petterssonandreas/cooking_thermometer/apps/ct/src/display.c

#include "display.h"

#include <zephyr/kernel.h>
#include <zephyr/device.h>
#include <zephyr/display/cfb.h>
#include <zephyr/drivers/display.h>
#include <stdio.h>

#include <zephyr/logging/log.h>
LOG_MODULE_REGISTER(ct_display, CONFIG_CT_DISPLAY_LOG_LEVEL);

#include "cttime.h"
#include "state.h"

#define FONT_IDX 1

static const struct device *dev = DEVICE_DT_GET(DT_CHOSEN(zephyr_display));

static K_THREAD_STACK_DEFINE(display_thread_stack, 1024);

static struct k_thread display_thread;


static void display_draw_no_probe(void)
{
    char s[16];
    snprintf(s, sizeof(s), "---");
    cfb_print(dev, s, 0, 24);
}

static void display_draw_battery_level(uint8_t battery_percentage)
{
    cfb_invert_area(dev, 109, 0, 17, 16);
    cfb_invert_area(dev, 111, 2, 13, 12);
    cfb_invert_area(dev, 126, 5, 2, 6);

    if (battery_percentage > 20) {
        cfb_invert_area(dev, 112, 4, 3, 9);
    }
    if (battery_percentage > 60) {
        cfb_invert_area(dev, 116, 4, 3, 9);
    }
    if (battery_percentage > 80) {
        cfb_invert_area(dev, 120, 4, 3, 9);
    }
}

static void display_fn(void *p1, void *p2, void *p3)
{
    UNUSED(p1);
    UNUSED(p2);
    UNUSED(p3);

    char s[16];

    while (true) {
        k_sleep(K_MSEC(100));

        /* Start by clearing */
        cfb_framebuffer_clear(dev, false);

        snprintf(s, sizeof(s), "%d", state.state);
        cfb_print(dev, s, 0, 0);

        switch (state.state) {
        case STATE_INIT:
            cfb_print(dev, "Init", 0, 24);
            break;

        case STATE_IDLE:
        case STATE_TARGET_TEMP_REACHED:
        case STATE_TARGET_TEMP_REACHED_ACKED:
            if (!state.probe_connected) {
                display_draw_no_probe();
            }
            else {
                display_draw_temperature(state.temperature);
            }
            break;

        case STATE_SET_TARGET_TEMP:
            if (state.blink) {
                snprintf(s, sizeof(s), "% 3d *C", state.target_temperature);
                cfb_print(dev, s, 0, 24);
            }
            break;

        default:
            cfb_print(dev, "state?", 0, 24);
            break;
        }

        display_draw_battery_level(state.battery_percentage);

        /* Do the actual drawing */
        cfb_framebuffer_finalize(dev);
    }
}

int display_init(void)
{
    uint16_t x_res;
    uint16_t y_res;
    uint16_t rows;
    uint8_t ppt;
    uint8_t font_width;
    uint8_t font_height;

    if (!device_is_ready(dev)) {
        LOG_ERR("Device %s not ready", dev->name);
        return -ENODEV;
    }

    if (display_set_pixel_format(dev, PIXEL_FORMAT_MONO10) != 0) {
        if (display_set_pixel_format(dev, PIXEL_FORMAT_MONO01) != 0) {
            LOG_ERR("Failed to set required pixel format");
            return -EINVAL;
        }
    }

    LOG_INF("Initialized %s", dev->name);

    if (cfb_framebuffer_init(dev)) {
        LOG_ERR("Framebuffer initialization failed!");
        return -ENODEV;
    }

    cfb_framebuffer_clear(dev, true);

    display_blanking_off(dev);

    x_res = cfb_get_display_parameter(dev, CFB_DISPLAY_WIDTH);
    y_res = cfb_get_display_parameter(dev, CFB_DISPLAY_HEIGH);
    rows = cfb_get_display_parameter(dev, CFB_DISPLAY_ROWS);
    ppt = cfb_get_display_parameter(dev, CFB_DISPLAY_PPT);

    if (cfb_get_font_size(dev, FONT_IDX, &font_width, &font_height))
    {
        LOG_ERR("Failed to get font for index %u", FONT_IDX);
        return -EBFONT;
    }
    cfb_framebuffer_set_font(dev, FONT_IDX);
    LOG_INF("font width %d, font height %d", font_width, font_height);

    LOG_INF("x_res %d, y_res %d, ppt %d, rows %d, cols %d", x_res, y_res, ppt, rows, cfb_get_display_parameter(dev, CFB_DISPLAY_COLS));

    // cfb_framebuffer_invert(dev);

    cfb_set_kerning(dev, 0);

    cfb_framebuffer_clear(dev, false);
    cfb_print(dev, "Booting", 0, 24);
    cfb_framebuffer_finalize(dev);

    /* Start display thread */
    k_thread_create(
        &display_thread,
        display_thread_stack,
        K_THREAD_STACK_SIZEOF(display_thread_stack),
        display_fn,
        NULL, NULL, NULL,
        K_LOWEST_APPLICATION_THREAD_PRIO,
        0,
        K_NO_WAIT);

    return 0;
}

void display_draw_time(void)
{
    int ret;
    struct rtc_time tm;

    ret = cttime_get_date_time(&tm);
    if (ret) {
        LOG_ERR("Failed to get time: %d", ret);
        return;
    }

    // LOG_INF("RTC date and time: %04d-%02d-%02d %02d:%02d:%02d", tm.tm_year + 1900,
    //     tm.tm_mon + 1, tm.tm_mday, tm.tm_hour, tm.tm_min, tm.tm_sec);

    char s[16];
    snprintf(s, sizeof(s), "%02d:%02d:%02d", tm.tm_hour, tm.tm_min, tm.tm_sec);

    cfb_print(dev, s, 0, 24);
}

void display_draw_voltage(int16_t mvolt, int16_t raw)
{
    char s[16];

    snprintf(s, sizeof(s), "v: %d", mvolt);
    cfb_print(dev, s, 0, 0);
    snprintf(s, sizeof(s), "r: %d", raw);
    cfb_print(dev, s, 0, 24);
}

void display_draw_temperature(int16_t temperature)
{
    char s[16];

    if (temperature == INT16_MIN) {
        snprintf(s, sizeof(s), "-99 *C");
    }
    else if (temperature == INT16_MAX) {
        snprintf(s, sizeof(s), "999 *C");
    }
    else {
        snprintf(s, sizeof(s), "% 3d *C", temperature);
    }
    cfb_print(dev, s, 0, 24);
}
